ziggekatten/m68k/m68k_bare_metal/mb68k/monitor.c

/**
 * @author (c) Mats Brorson ()
 *             2023-2024, Sweden
 *
 * @brief Code for firmware monitor such as reading and writing to memory
 *
 *
 * @license The MIT License (MIT)
 *
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
 * THE SOFTWARE IS PROVIDED "AS IS", WITHOUT WARRANTY OF ANY KIND, EXPRESS OR
 * IMPLIED, INCLUDING BUT NOT LIMITED TO THE WARRANTIES OF MERCHANTABILITY,
 * FITNESS FOR A PARTICULAR PURPOSE AND NONINFRINGEMENT. IN NO EVENT SHALL THE
 * AUTHORS OR COPYRIGHT HOLDERS BE LIABLE FOR ANY CLAIM, DAMAGES OR OTHER
 * LIABILITY, WHETHER IN AN ACTION OF CONTRACT, TORT OR OTHERWISE, ARISING FROM,
 * OUT OF OR IN CONNECTION WITH THE SOFTWARE OR THE USE OR OTHER DEALINGS IN
 * THE SOFTWARE.
 */

#include "monitor.h"
#include "machine.h"
#include <stdint.h>
#include <stdbool.h>
#include <stdio.h>
#include <string.h>
#include <stdlib.h>

const char *fwhelp = HELP_H;                        // Help text 
const char *header = READ_MEM_HEADER;               // Header when reading memory

/* reset serial buffer. ToDo: handle selectable buffer */
void resetbuffer(serialstruct *buf) {
    memset(buf->buf, 0, sizeof(buf->buf));            // Reset input buffer completely!!! Otherwise bad things WILL happen....                
    buf->idx = 0;                                     // Reset buffer index
}

/* Print invalid command*/
void printinvalid(serialstruct *buf) {
    printf("Invalid command: %s\n",(char*)buf->buf);
    printf("Type 'h' for help.\n %s", prompt);
    resetbuffer(buf);    
}

/* Print help message and reset input buffer */
void printhelp(serialstruct *buf) {
    printf("%s\n%s", fwhelp, prompt);
    resetbuffer(buf);
}

// Used to parse an read command
void parseread(serialstruct *buf) {
    printf("%s\n%s", fwhelp, prompt);
    resetbuffer(buf);
}

/* Help struct*/
ParseStruct c_help = {"help ", printhelp};
/* Read struct */
ParseStruct c_read = {"read ", parseread};
/* Put the structs in an array */
ParseStruct *parser[2] = {&c_help, &c_read};

void readmem(uint32_t baseadr) {
    printf("%s", header);
    volatile uint8_t *p = (uint8_t *)baseadr;       // Pointer to base address to read
    int rows;                                       // Rows to return. set in for loop
    for (rows = 0; rows < 20; rows++){
        printf("%#010x: %02x %02x %02x %02x %02x %02x %02x %02x %02x %02x %02x %02x %02x %02x %02x %02x\n", (uint32_t)p, 
            *p, *(p+1), *(p+2), *(p+3),
            *(p+4), *(p+5), *(p+6), *(p+7),
            *(p+8), *(p+9), *(p+10), *(p+11),
            *(p+12), *(p+13), *(p+14), *(p+15)
            );
        p = p + 16;                                 // Increment address pointer
    } 
    printf("\n%s", prompt);
}


/* Pseudo parse function for incoming data from keyboard or serial communication 
* This will be an true tree parser at some point.... */
void parsecommand(serialstruct *buf) {
    //c_help.parsefunc(buf);
    switch (buf->buf[0]) {
        case FW_HELP:
            printf("%s\n%s", fwhelp, prompt);
            resetbuffer(buf);
            break;
        default:
            //\b\e[K\n
            printf("Invalid command: %s\n",(char*)buf->buf);
            printf("Type 'h' for help.\n %s", prompt);
            readmem(0x00100010);
            resetbuffer(buf);
            break;
        }
}
