ziggekatten/m68k/code/firmware/src/include/memcheck.h

/*
* @Author: Mats Brorson
* @Date: 2023-01-27
* 
* @Description: Function prototypes for memory chech routines and error handling / panic.
*/
#ifndef _MEM_CHECK_H
#define _MEM_CHECK_H

/* Prototype for checking memory */
mem_check();


#endif
