ziggekatten/m68k/code/firmware/src/serial.c

/**
* @Author: Mats Brorson
* @Date: 2023-01-27
* 
* @Description: Functions to initialize serial communication
*/
#include "include/hwdefs.h"
#include "include/serial.h"

/*prototypes for initializing Serial commmunication */
void Init_Serial(void)
{
    while(1);
}
