ziggekatten/m68k/code/firmware/src/include/serial.h

/*
* @Author: Mats Brorson
* @Date: 2023-01-27
* 
* @Description: Functions to initialize and start serial communications
*/
#ifndef _MB68K_SERIAL_H
#define _MB68K_SERIAL_H

/*prototype for initializing Serial commmunication function in DUART */
void Init_Serial(void);


#endif
