ziggekatten/m68k/code/firmware/src/include/utils.h

/*
* @Author: Mats Brorson
* @Date: 2023-01-27
* 
* @Description: Function prototypes for various utilities needed to make life easier when not using stdlibc.
*/

#ifndef _MB68K_UTILS_H
#define _MB68K_UTILS_H

/* Prototype to provide hex rpresentation if integers for ASCII output */
char *itohexa(char *dest, unsigned x);

#endif
